Vahegian/General-Interactive-Automation-Network/Summer Research/pics/milestones.PNG

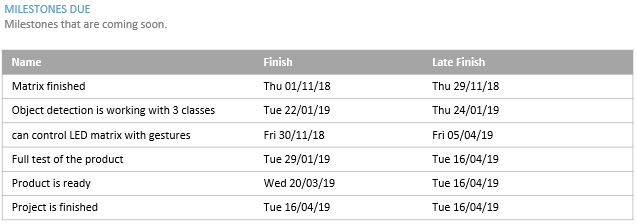
Summer Research/pics/milestones.PNG
