Vahegian/General-Interactive-Automation-Network/The Project/Research and Files/Files/General/four_25x25_matrices.jpg

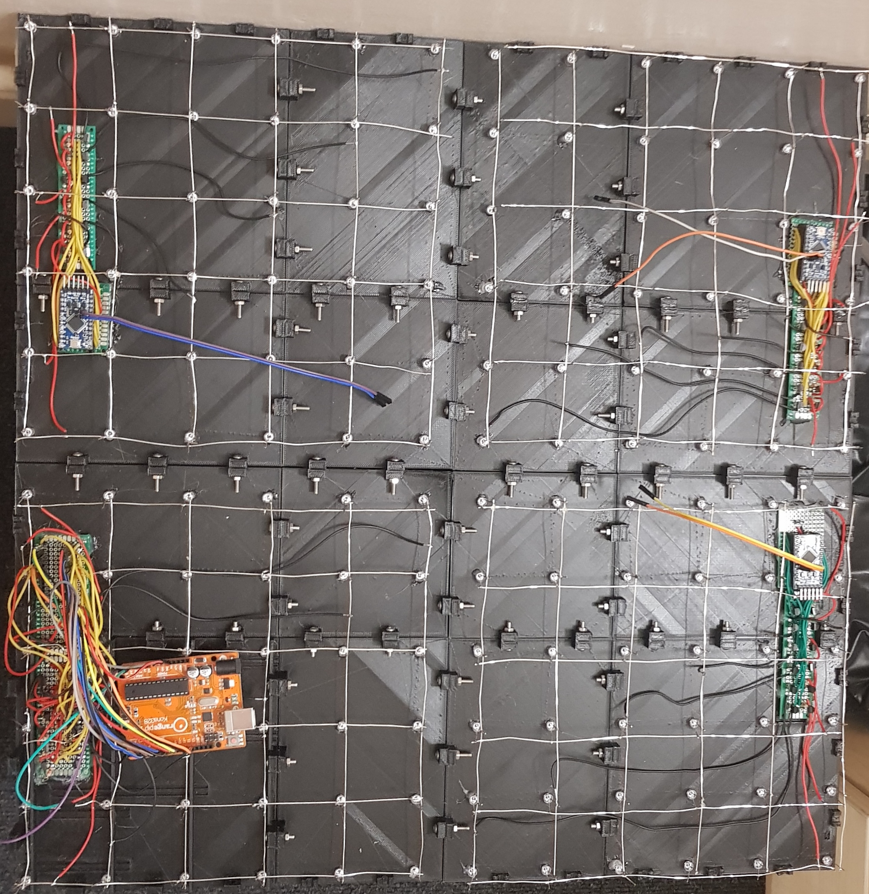
The Project/Research and Files/Files/General/four_25x25_matrices.jpg
