Vahegian/General-Interactive-Automation-Network/The Project/Research and Files/Files/Matrix/Connectors/power_connector_back.jpg

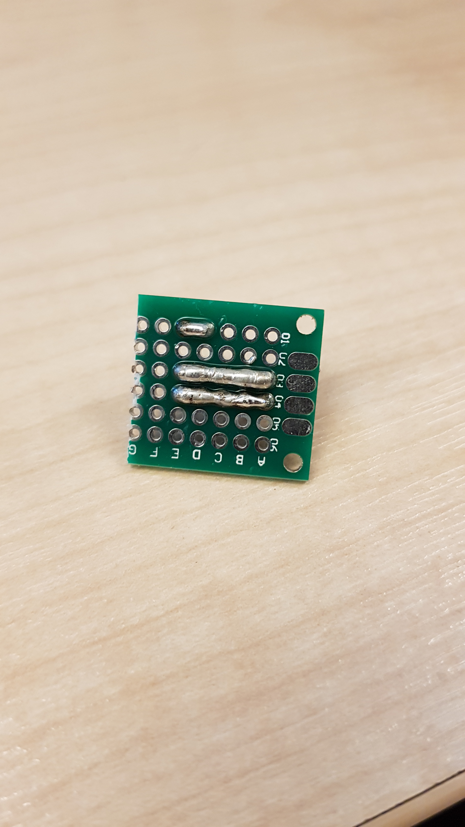
The Project/Research and Files/Files/Matrix/Connectors/power_connector_back.jpg
