Vahegian/General-Interactive-Automation-Network/The Project/Research and Files/Files/Matrix/Connectors/UNO_to_mini_convertor.jpg

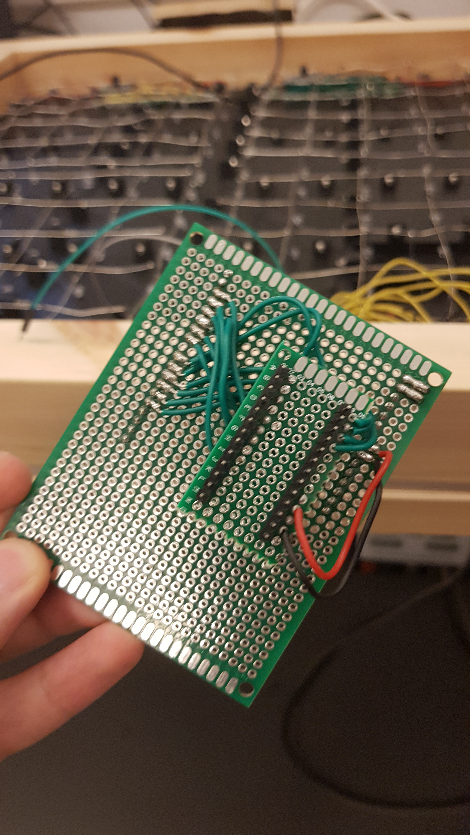
The Project/Research and Files/Files/Matrix/Connectors/UNO_to_mini_convertor.jpg
