Vahegian/General-Interactive-Automation-Network/The Project/Research and Files/Files/Matrix/Connectors/UNO_to_mini_convertor_2.jpg

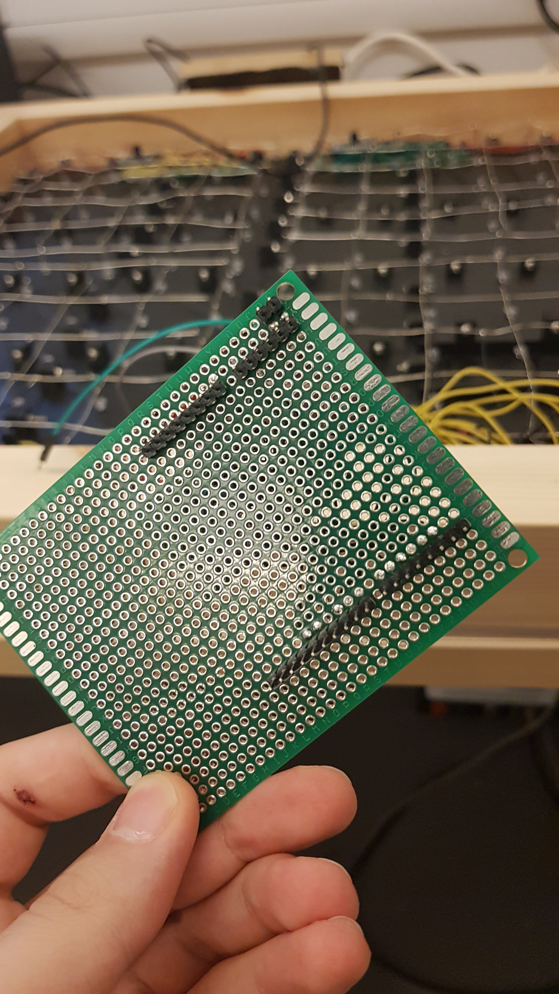
The Project/Research and Files/Files/Matrix/Connectors/UNO_to_mini_convertor_2.jpg
