Vahegian/General-Interactive-Automation-Network/The Project/Research and Files/Files/Matrix/LED_controller_circuit.jpg

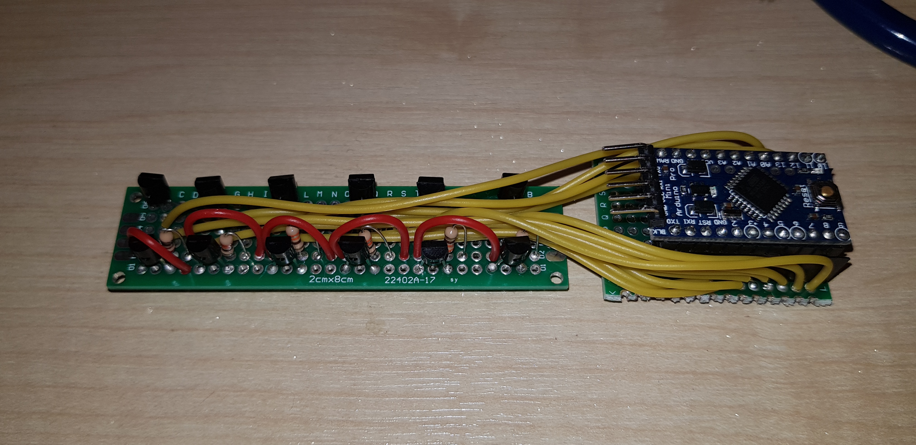
The Project/Research and Files/Files/Matrix/LED_controller_circuit.jpg
