Vahegian/General-Interactive-Automation-Network/The Project/Research and Files/Files/Matrix/resetButton/2.jpg

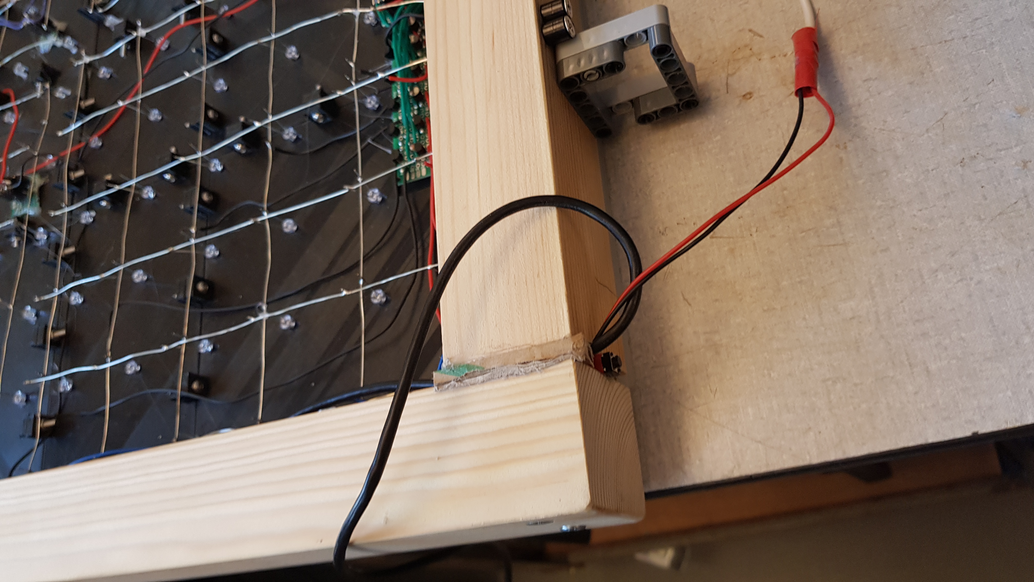
The Project/Research and Files/Files/Matrix/resetButton/2.jpg
