Vahegian/General-Interactive-Automation-Network/The Project/Research and Files/Files/Matrix/Matrices_assembled.jpg

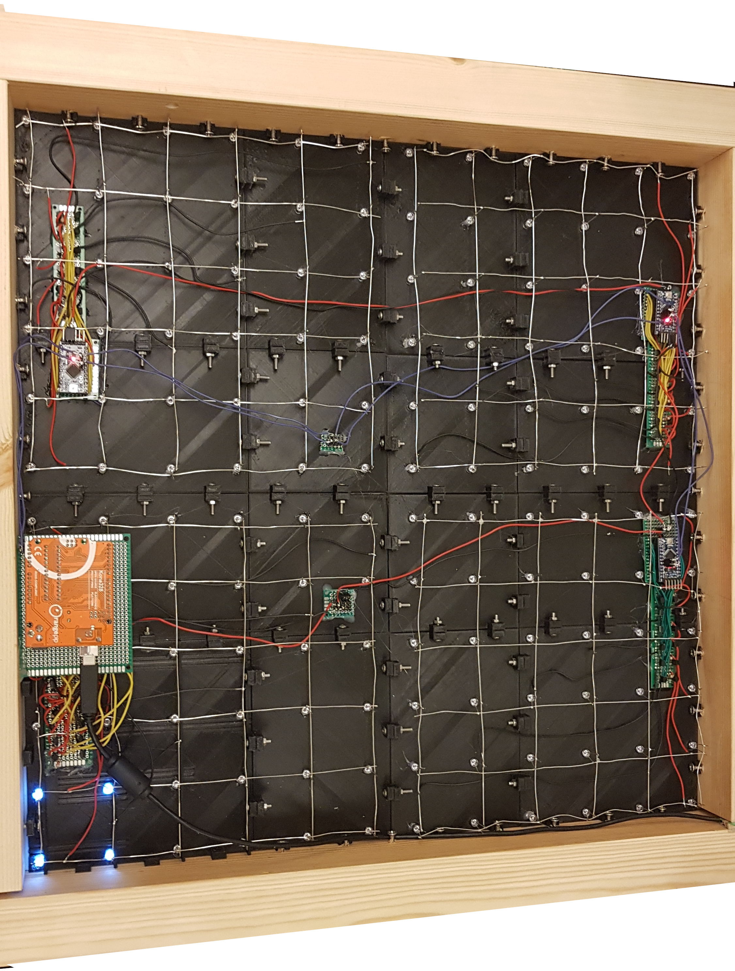
The Project/Research and Files/Files/Matrix/Matrices_assembled.jpg
